TrentConley/globe/engineering-assets/coverage-cities.png

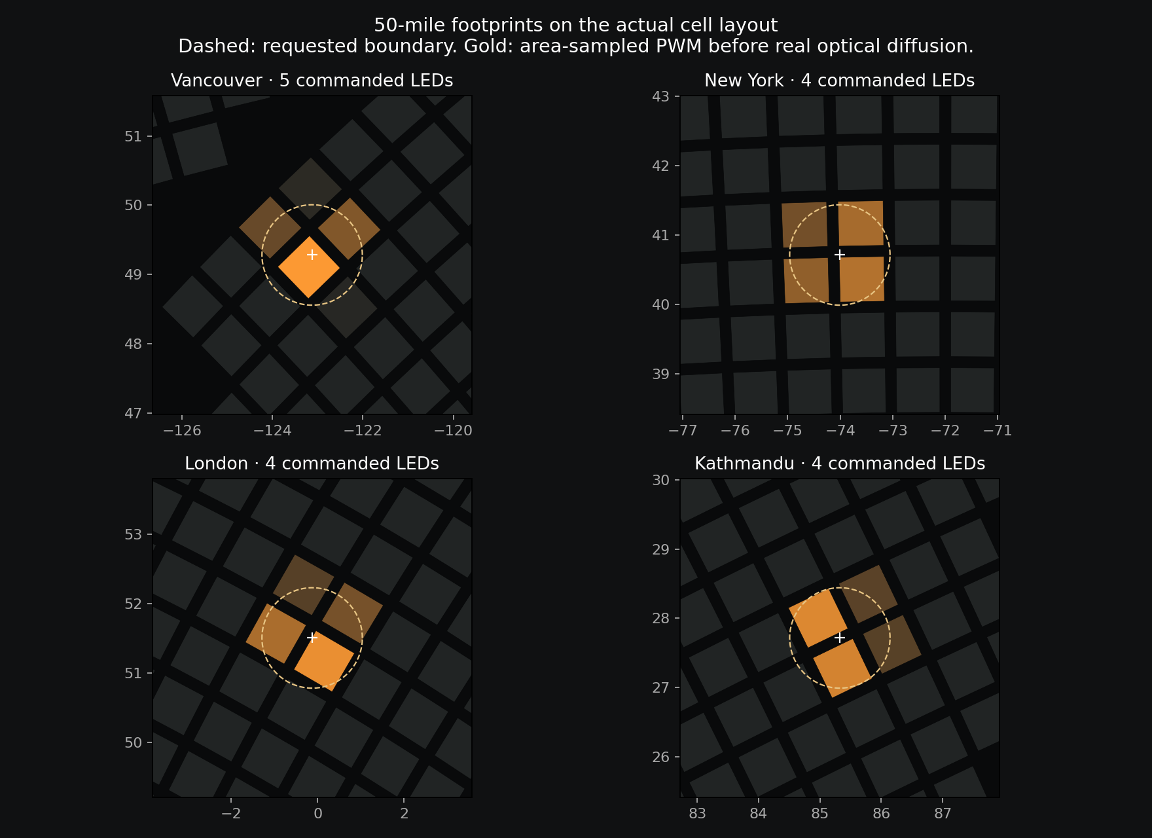
engineering-assets/coverage-cities.png
