TrentConley/globe/engineering-assets/engineering-prototype.png

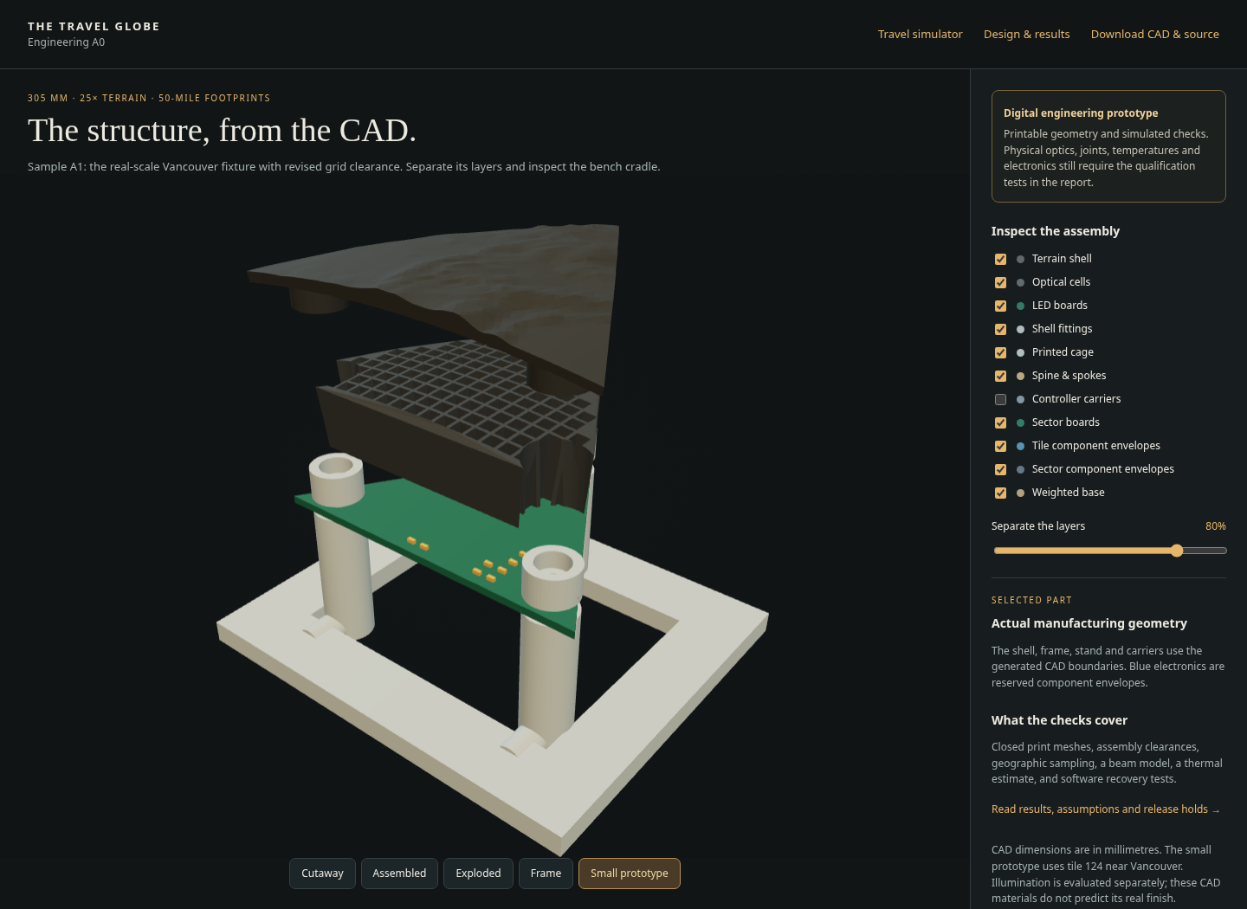
engineering-assets/engineering-prototype.png
