TrentConley/globe/engineering-assets/structural-gravity.png

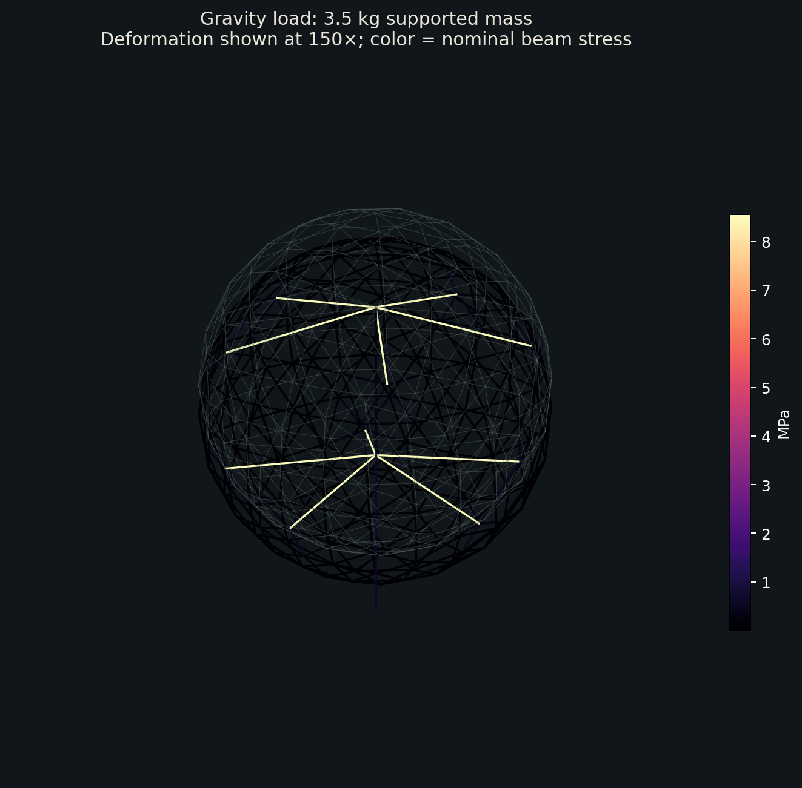
engineering-assets/structural-gravity.png
