TrentConley/globe/engineering-assets/thermal-sensitivity.png

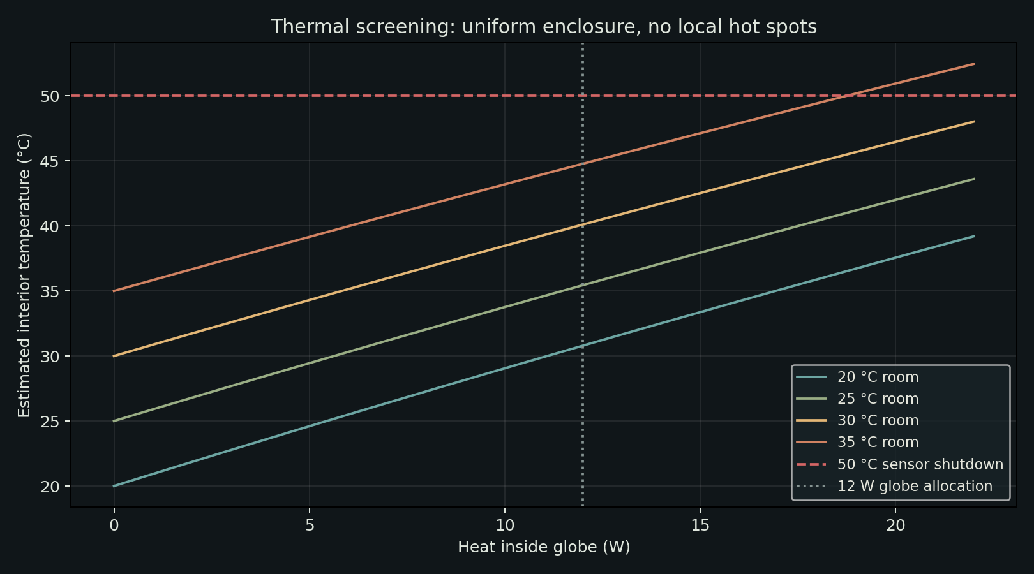
engineering-assets/thermal-sensitivity.png
