TrentConley/globe/build-assets/structure-cutaway.png

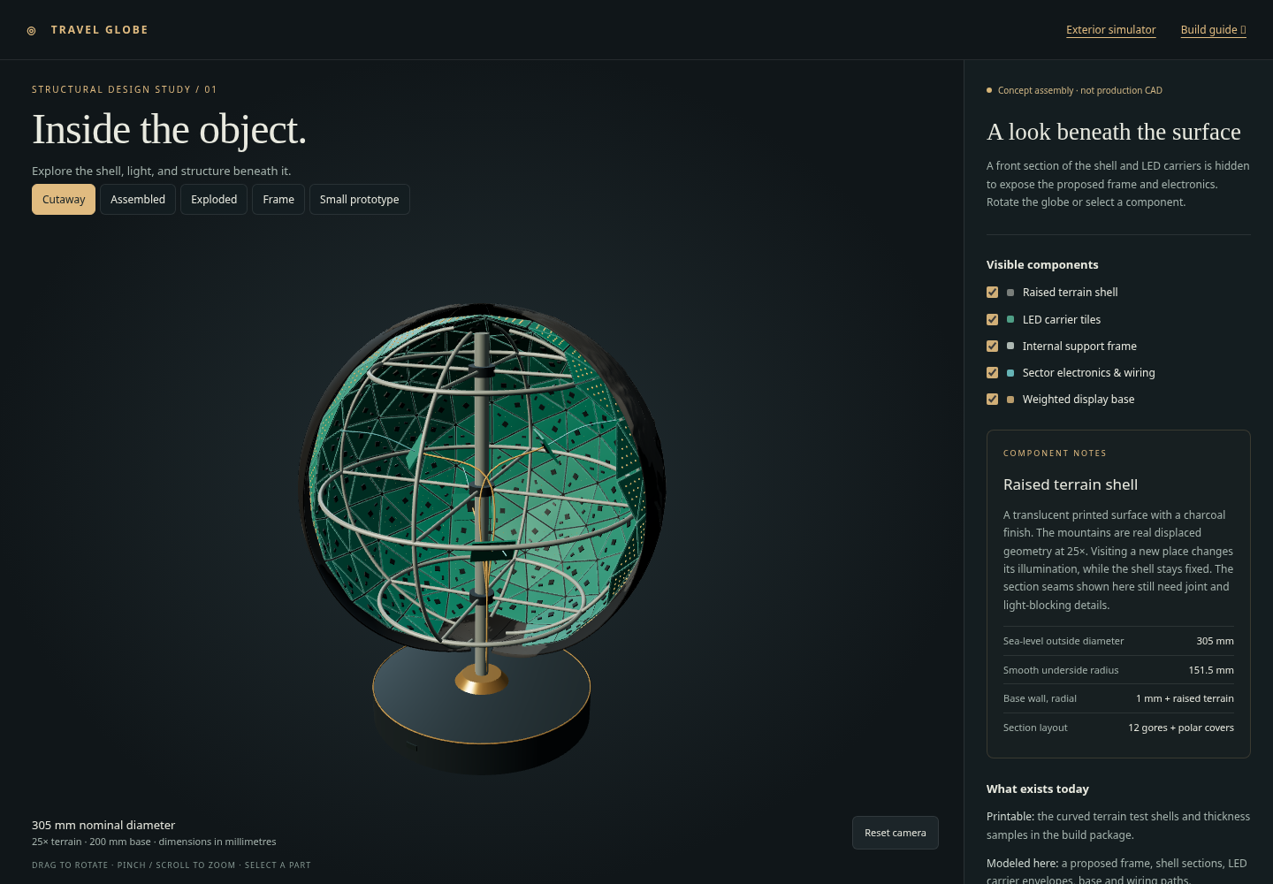
build-assets/structure-cutaway.png
