TrentConley/globe/build-assets/structure-prototype.png

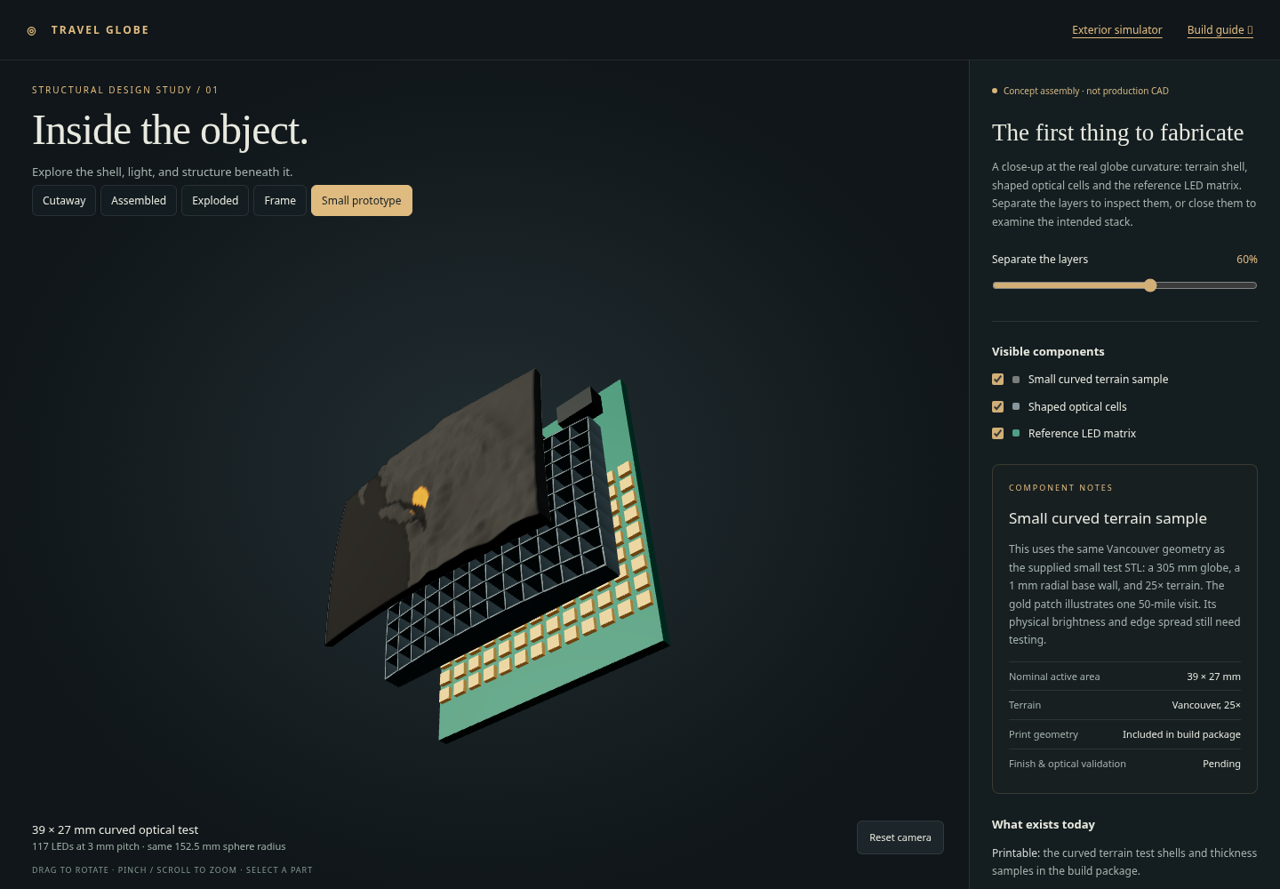
build-assets/structure-prototype.png
